PostTenebrasLab/PTL-IR_remote/presentation_workshop/images/bonne-soudure1.jpg

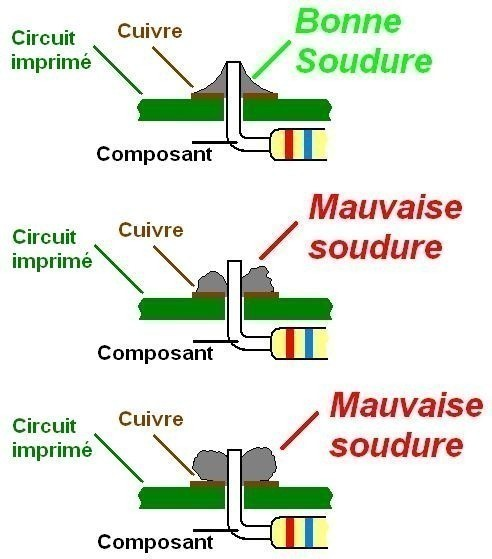
presentation_workshop/images/bonne-soudure1.jpg
