PostTenebrasLab/PTL-IR_remote/presentation_workshop/images/bonne-soudure.jpg

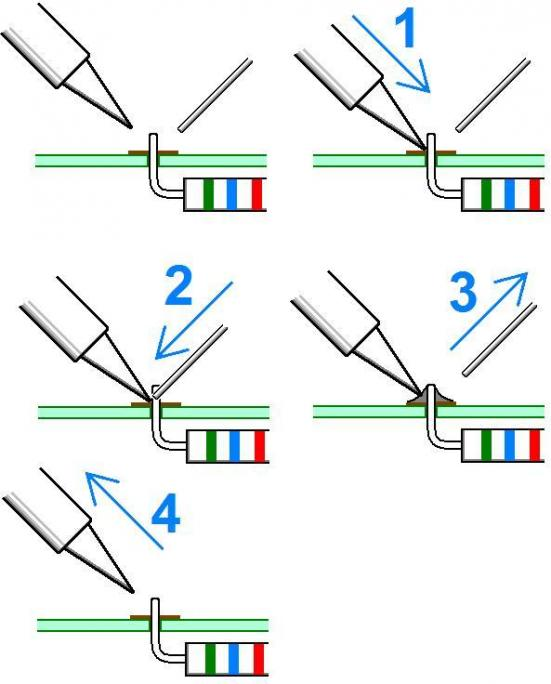
presentation_workshop/images/bonne-soudure.jpg
