PostTenebrasLab/PTL-IR_remote/presentation_workshop/images/PTL-IR_remote_04.png

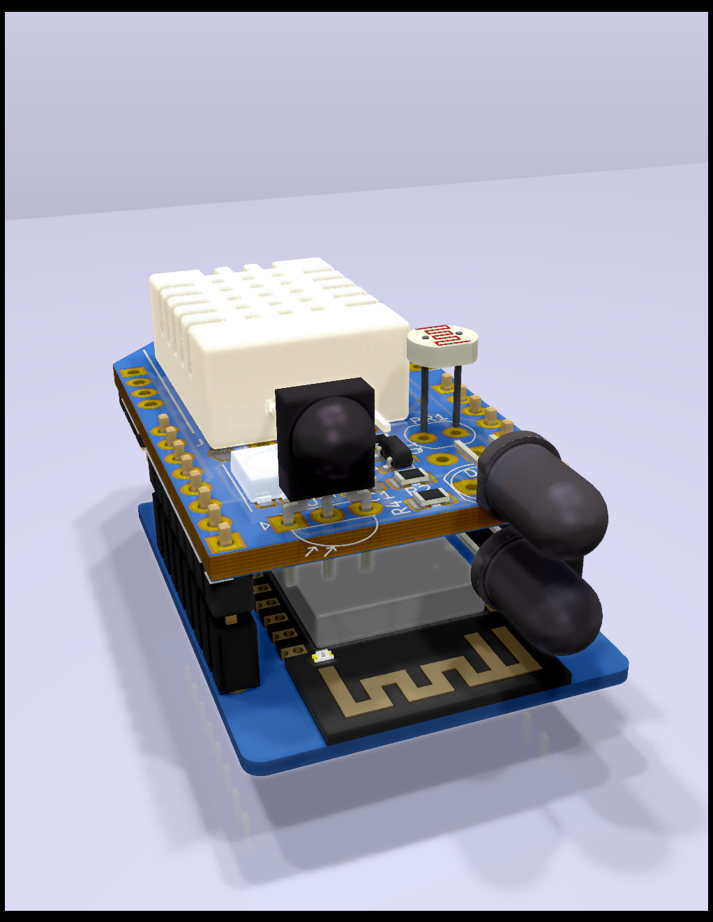
presentation_workshop/images/PTL-IR_remote_04.png
