PostTenebrasLab/PTL-IR_remote/presentation_workshop/images/PTL-IR_remote_case_01.png

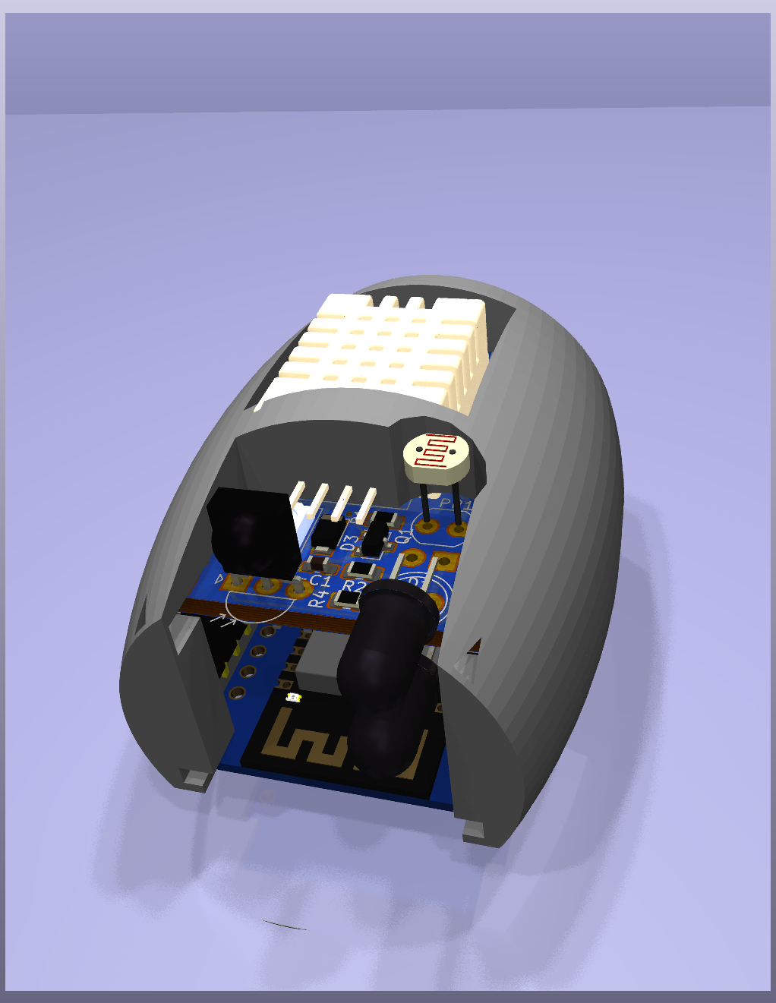
presentation_workshop/images/PTL-IR_remote_case_01.png
