PostTenebrasLab/PTL-IR_remote/presentation_workshop/images/PTL-IR_remote_case_03.png

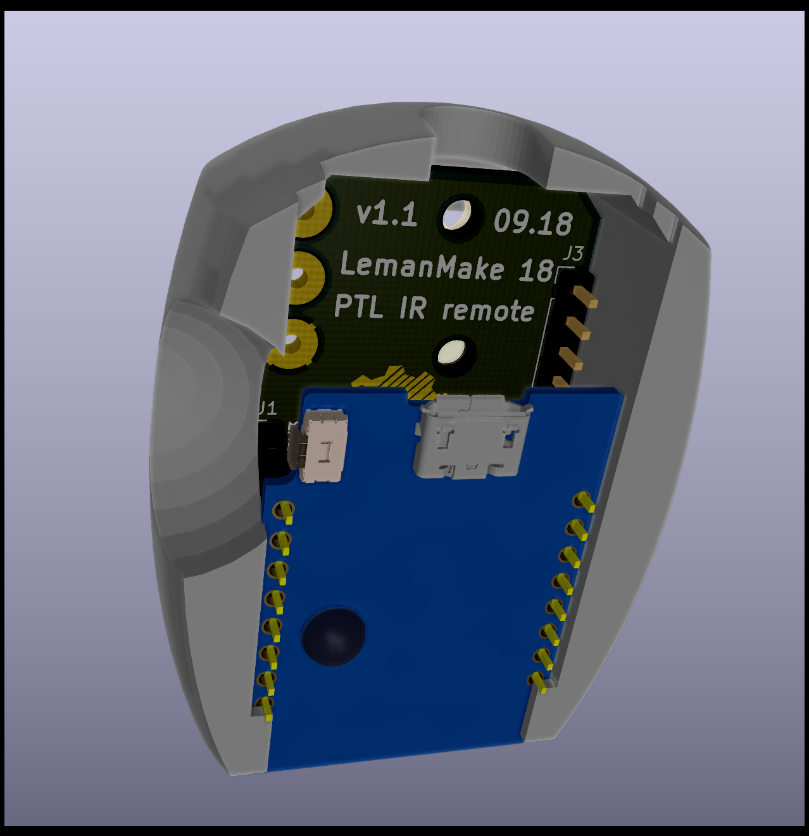
presentation_workshop/images/PTL-IR_remote_case_03.png
