PostTenebrasLab/PTL-IR_remote/presentation_workshop/pics/componants.jpg

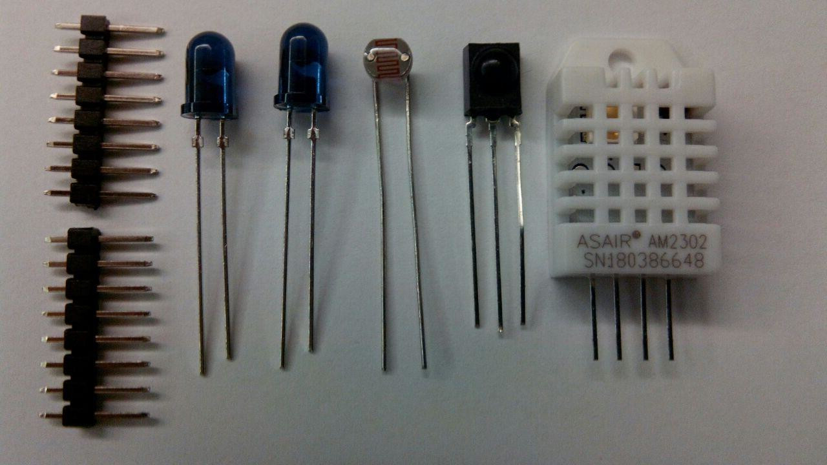
presentation_workshop/pics/componants.jpg
