PostTenebrasLab/PTL-IR_remote/presentation_workshop/pics/exemple_soudures.png

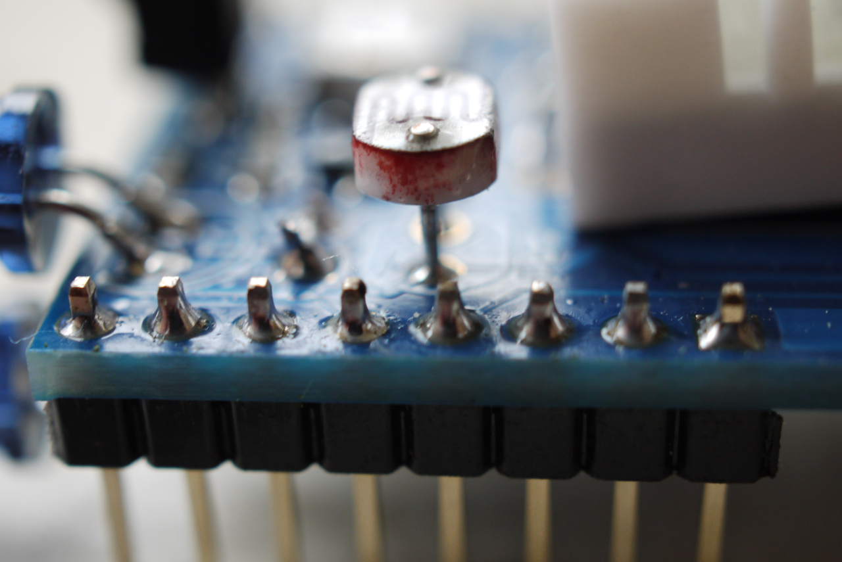
presentation_workshop/pics/exemple_soudures.png
