PostTenebrasLab/PTL-IR_remote/presentation_workshop/pics/headers.png

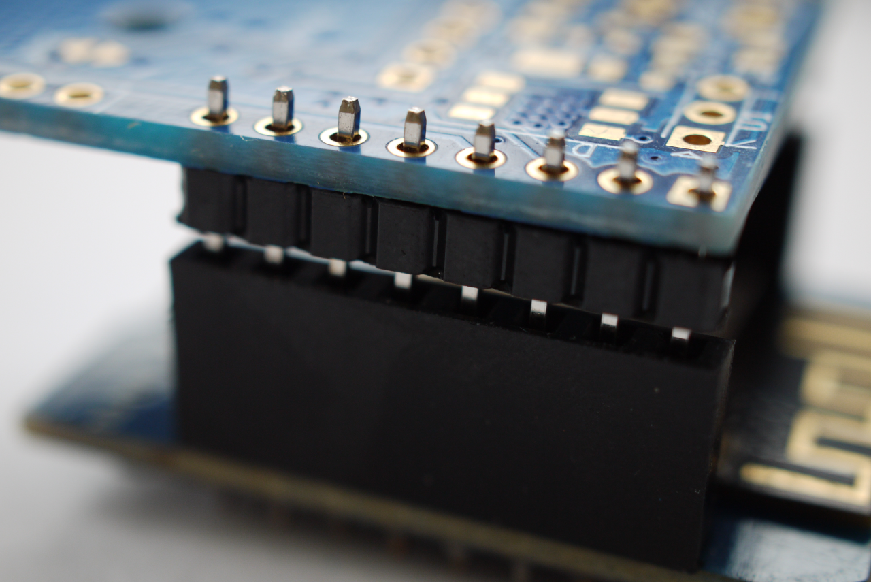
presentation_workshop/pics/headers.png
