PostTenebrasLab/PTL-IR_remote/presentation_workshop/pics/leds1.png

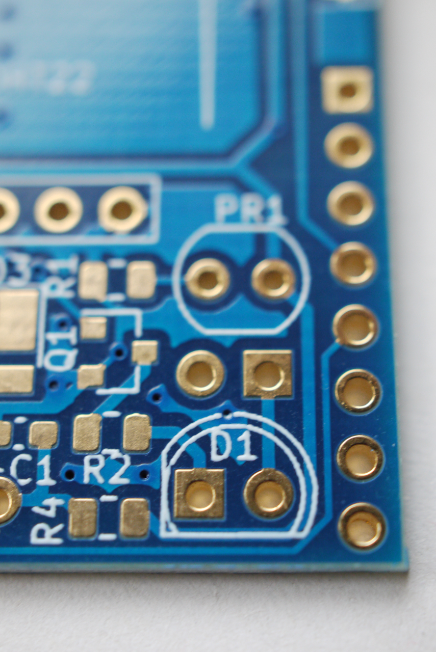
presentation_workshop/pics/leds1.png
