PostTenebrasLab/PTL-IR_remote/presentation_workshop/pics/leds2.png

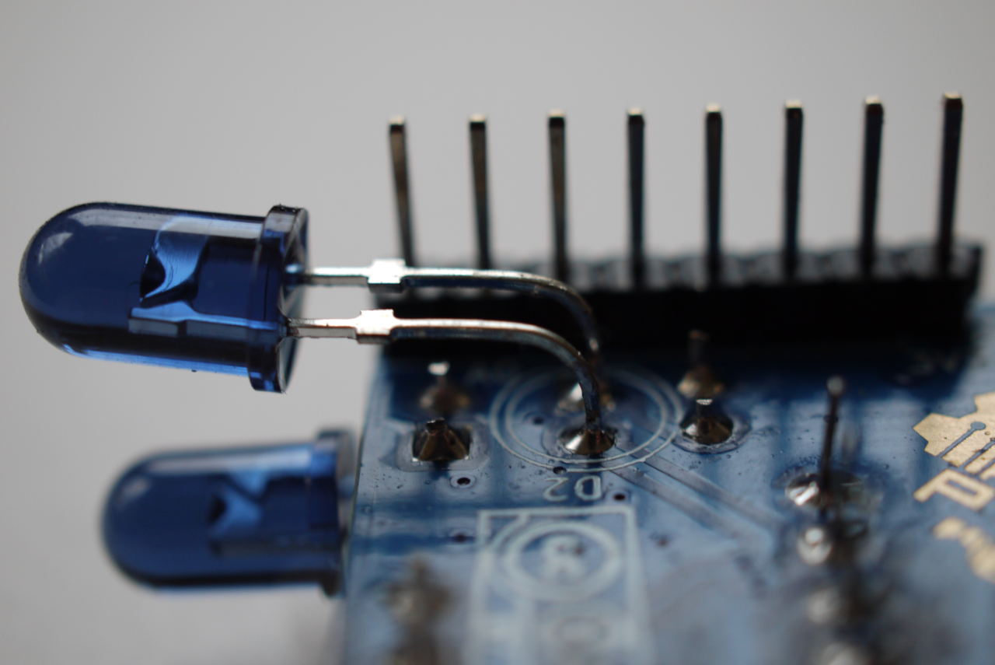
presentation_workshop/pics/leds2.png
