PostTenebrasLab/PTL-IR_remote/presentation_workshop/pics/photores_1.png

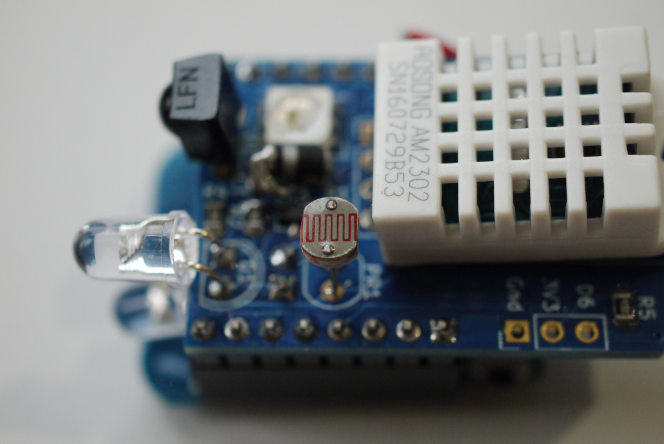
presentation_workshop/pics/photores_1.png
