PostTenebrasLab/PTL-IR_remote/presentation_workshop/pics/photores_2.png

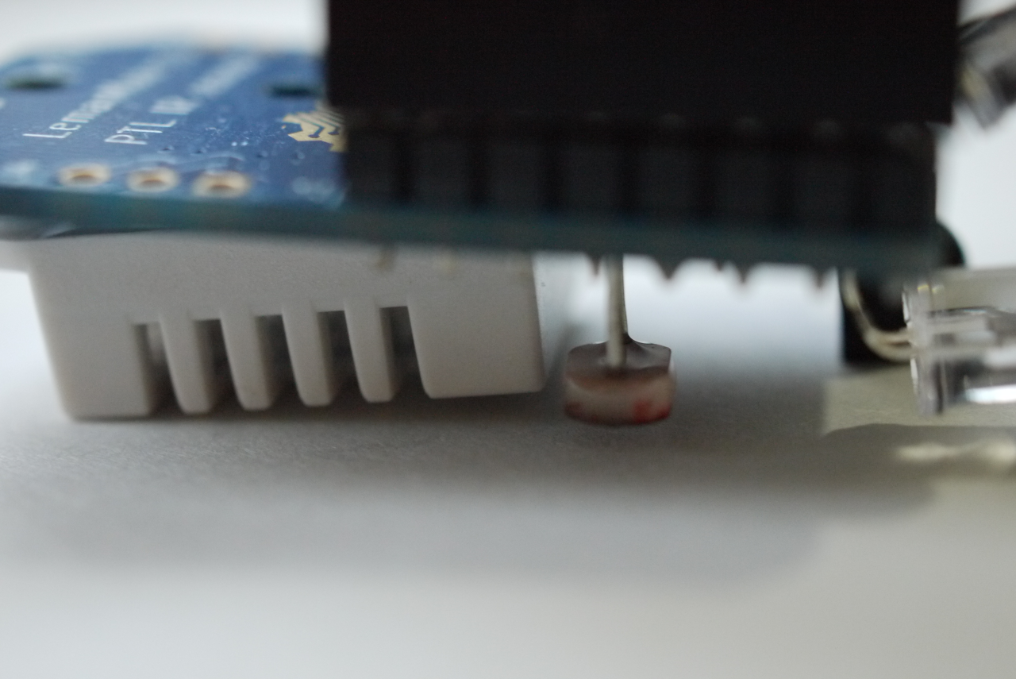
presentation_workshop/pics/photores_2.png
